albertKCR/stm32-dual-channel-smu/DWIN_display_interface/DWIN_SET/01_dwin_soloCh.jpg

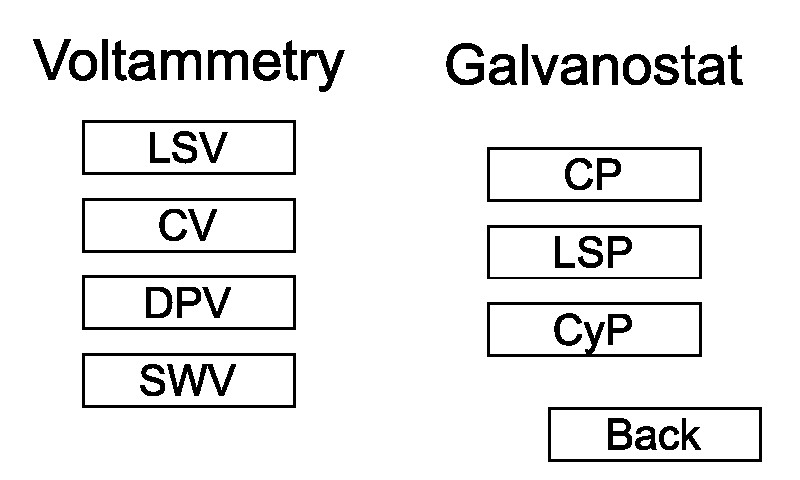
DWIN_display_interface/DWIN_SET/01_dwin_soloCh.jpg
