albertKCR/stm32-dual-channel-smu/DWIN_display_interface/DWIN_SET/03_dwin_CV.jpg

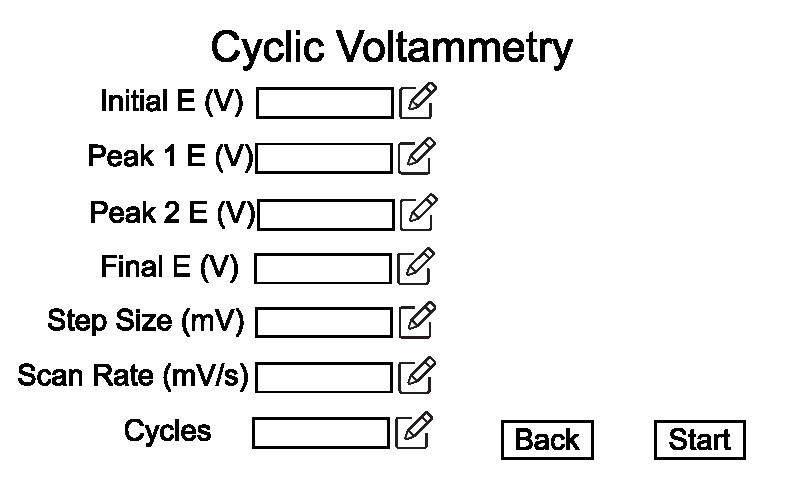
DWIN_display_interface/DWIN_SET/03_dwin_CV.jpg
