albertKCR/stm32-dual-channel-smu/DWIN_display_interface/DWIN_SET/05_dwin_SWV.jpg

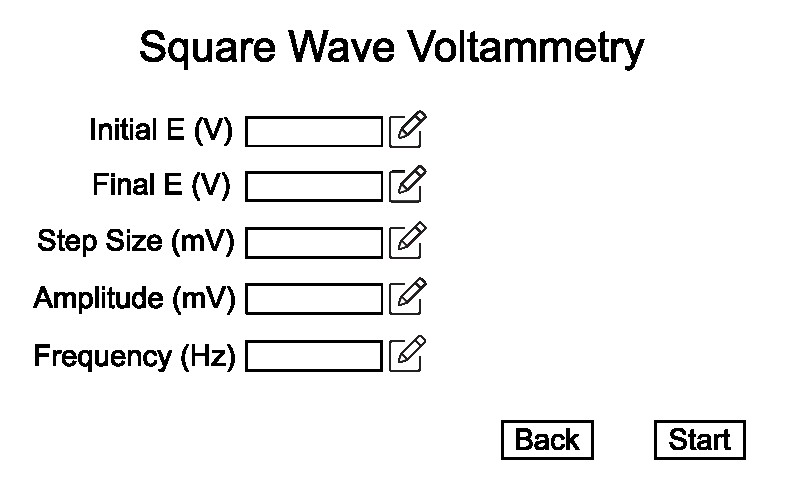
DWIN_display_interface/DWIN_SET/05_dwin_SWV.jpg
