albertKCR/stm32-dual-channel-smu/DWIN_display_interface/DWIN_SET/06_dwin_CP.jpg

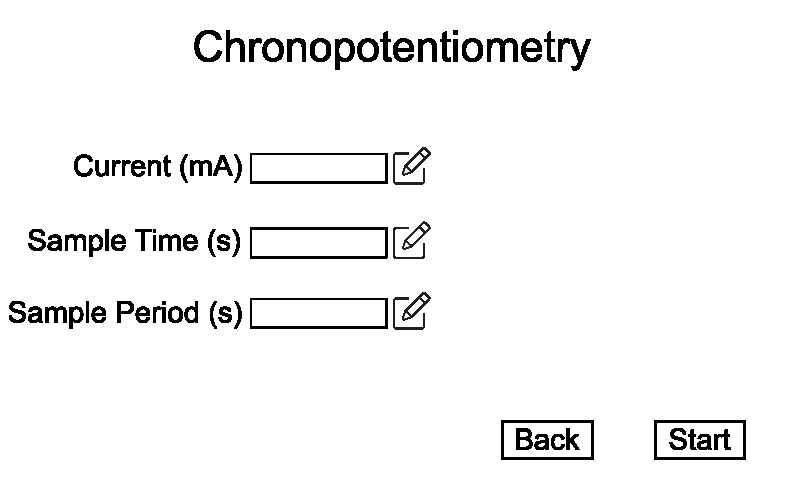
DWIN_display_interface/DWIN_SET/06_dwin_CP.jpg
