albertKCR/stm32-dual-channel-smu/DWIN_display_interface/DWIN_SET/09_dwin_numPad.jpg

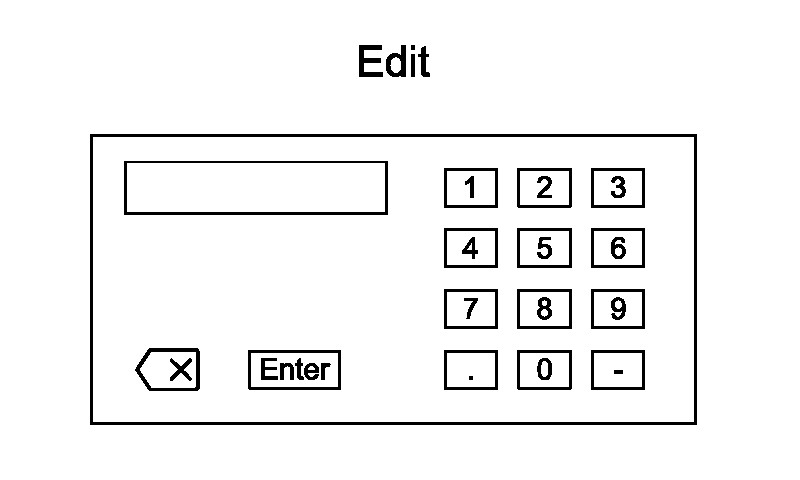
DWIN_display_interface/DWIN_SET/09_dwin_numPad.jpg
